gchinellato/Self-Balance-Robot/Arduino/Examples/IMU/Barom/GY80_BMP085.cpp

// Programa : Teste BMP085 - Barometro / temperatura
// Adaptacoes : Arduino e Cia

/*Based largely on code by  Jim Lindblom
 Get pressure, altitude, and temperature from the BMP085.
 Serial.print it out at 9600 baud to serial monitor.
*/

#include <Wire.h>

//Define o endereco I2C do BMP085 - 0x77 ou 119 em decimal
#define BMP085_ADDRESS 0x77  

const unsigned char OSS = 0;  // Oversampling Setting

// Calibration values
int ac1;
int ac2;
int ac3;
unsigned int ac4;
unsigned int ac5;
unsigned int ac6;
int b1;
int b2;
int mb;
int mc;
int md;

// b5 is calculated in bmp085GetTemperature(...), this 
// variable is also used in bmp085GetPressure(...)
// so ...Temperature(...) must be called before ...Pressure(...).
long b5; 

void setup()
{
  Serial.begin(9600);
  Wire.begin();
  // Inicializa o BMP085
  bmp085Calibration();
}

void loop()
{
  // Chama a rotina que calcula a temperatura
  // Esta rotina DEVE ser executada primeiro
  float temperature = bmp085GetTemperature(bmp085ReadUT());
  // Chama a rotina que calcula a pressao
  float pressure = bmp085GetPressure(bmp085ReadUP());
  // Chama a rotina que calcula atmosfera
  float atm = pressure / 101325; 
  // Chama a rotina que calcula a altitude
  float altitude = calcAltitude(pressure); 

  Serial.print("Temperatura: ");
  // Mostra a temperatura com 2 casas decimais
  Serial.print(temperature, 2); 
  Serial.println(" C");

  Serial.print("Pressao: ");
  Serial.print(pressure, 0); 
  Serial.println(" Pa");

  Serial.print("Atmosfera padrao : ");
  // Mostra o valor com 4 casas decimais
  Serial.println(atm, 4); //display 4 decimal places

  Serial.print("Altitude: ");
  // Mostra o valor com 2 casas decimais
  Serial.print(altitude, 2); 
  Serial.println(" M");

  Serial.println();

  //Aguarda 5 segundos e reinicia o processo
  delay(5000);
}

// Armazena todos os valores de calibracao do BMP085 em 
// variaveis globais. Valores de calibracao sao exigidos para
// calcular temperatura e pressao
// Esta funcao deve ser chamada/acionada no inicio do programa
void bmp085Calibration()
{
  ac1 = bmp085ReadInt(0xAA);
  ac2 = bmp085ReadInt(0xAC);
  ac3 = bmp085ReadInt(0xAE);
  ac4 = bmp085ReadInt(0xB0);
  ac5 = bmp085ReadInt(0xB2);
  ac6 = bmp085ReadInt(0xB4);
  b1 = bmp085ReadInt(0xB6);
  b2 = bmp085ReadInt(0xB8);
  mb = bmp085ReadInt(0xBA);
  mc = bmp085ReadInt(0xBC);
  md = bmp085ReadInt(0xBE);
}

// Calcula a temperatura em graus C
float bmp085GetTemperature(unsigned int ut)
{
  long x1, x2;

  x1 = (((long)ut - (long)ac6)*(long)ac5) >> 15;
  x2 = ((long)mc << 11)/(x1 + md);
  b5 = x1 + x2;

  float temp = ((b5 + 8)>>4);
  temp = temp /10;

  return temp;
}

// Calcula a pressao. Os valores de calibracao devem ser conhecidos
// b5 tambem eh exigido, logo a funcao bmp085GetTemperature(...) deve
// ser executada primeiro.
// Funcao retorna pressao em unidades de Pa
long bmp085GetPressure(unsigned long up){
  long x1, x2, x3, b3, b6, p;
  unsigned long b4, b7;

  b6 = b5 - 4000;
  // Calcula B3
  x1 = (b2 * (b6 * b6)>>12)>>11;
  x2 = (ac2 * b6)>>11;
  x3 = x1 + x2;
  b3 = (((((long)ac1)*4 + x3)<<OSS) + 2)>>2;

  // Calcula B4
  x1 = (ac3 * b6)>>13;
  x2 = (b1 * ((b6 * b6)>>12))>>16;
  x3 = ((x1 + x2) + 2)>>2;
  b4 = (ac4 * (unsigned long)(x3 + 32768))>>15;

  b7 = ((unsigned long)(up - b3) * (50000>>OSS));
  if (b7 < 0x80000000)
    p = (b7<<1)/b4;
  else
    p = (b7/b4)<<1;

  x1 = (p>>8) * (p>>8);
  x1 = (x1 * 3038)>>16;
  x2 = (-7357 * p)>>16;
  p += (x1 + x2 + 3791)>>4;

  long temp = p;
  return temp;
}

// Read 1 byte from the BMP085 at 'address'
char bmp085Read(unsigned char address)
{
  unsigned char data;

  Wire.beginTransmission(BMP085_ADDRESS);
  Wire.write(address);
  Wire.endTransmission();

  Wire.requestFrom(BMP085_ADDRESS, 1);
  while(!Wire.available())
    ;

  return Wire.read();
}

// Read 2 bytes from the BMP085
// First byte will be from 'address'
// Second byte will be from 'address'+1
int bmp085ReadInt(unsigned char address)
{
  unsigned char msb, lsb;

  Wire.beginTransmission(BMP085_ADDRESS);
  Wire.write(address);
  Wire.endTransmission();

  Wire.requestFrom(BMP085_ADDRESS, 2);
  while(Wire.available()<2)
    ;
  msb = Wire.read();
  lsb = Wire.read();

  return (int) msb<<8 | lsb;
}

// Read the uncompensated temperature value
unsigned int bmp085ReadUT(){
  unsigned int ut;

  // Write 0x2E into Register 0xF4
  // This requests a temperature reading
  Wire.beginTransmission(BMP085_ADDRESS);
  Wire.write(0xF4);
  Wire.write(0x2E);
  Wire.endTransmission();

  // Wait at least 4.5ms
  delay(5);

  // Read two bytes from registers 0xF6 and 0xF7
  ut = bmp085ReadInt(0xF6);
  return ut;
}

// Read the uncompensated pressure value
unsigned long bmp085ReadUP(){

  unsigned char msb, lsb, xlsb;
  unsigned long up = 0;

  // Write 0x34+(OSS<<6) into register 0xF4
  // Request a pressure reading w/ oversampling setting
  Wire.beginTransmission(BMP085_ADDRESS);
  Wire.write(0xF4);
  Wire.write(0x34 + (OSS<<6));
  Wire.endTransmission();

  // Wait for conversion, delay time dependent on OSS
  delay(2 + (3<<OSS));

  // Read register 0xF6 (MSB), 0xF7 (LSB), and 0xF8 (XLSB)
  msb = bmp085Read(0xF6);
  lsb = bmp085Read(0xF7);
  xlsb = bmp085Read(0xF8);

  up = (((unsigned long) msb << 16) | ((unsigned long) lsb << 8) | (unsigned long) xlsb) >> (8-OSS);

  return up;
}

void writeRegister(int deviceAddress, byte address, byte val) {
  Wire.beginTransmission(deviceAddress); // start transmission to device 
  Wire.write(address);       // send register address
  Wire.write(val);         // send value to write
  Wire.endTransmission();     // end transmission
}

int readRegister(int deviceAddress, byte address){

  int v;
  Wire.beginTransmission(deviceAddress);
  Wire.write(address); // register to read
  Wire.endTransmission();

  Wire.requestFrom(deviceAddress, 1); // read a byte

  while(!Wire.available()) {
    // waiting
  }

  v = Wire.read();
  return v;
}

float calcAltitude(float pressure)
{
  float A = pressure/101325;
  float B = 1/5.25588;
  float C = pow(A,B);
  C = 1 - C;
  C = C /0.0000225577;

  return C;
}
