gchinellato/Self-Balance-Robot/nfs-server/modules/ComputerVison/Test/stream.py

#!/usr/bin/python

import cv2
import urllib
import numpy as np
 
stream=urllib.urlopen('http://192.168.1.49:8080/?action=stream')
bytes=''
while True:
    bytes+=stream.read(1024)
    a = bytes.find('\xff\xd8')
    b = bytes.find('\xff\xd9')
    if a!=-1 and b!=-1:
        jpg = bytes[a:b+2]
        bytes= bytes[b+2:]
        i = cv2.imdecode(np.fromstring(jpg, dtype=np.uint8),cv2.CV_LOAD_IMAGE_COLOR)
        cv2.imshow('i',i)
        if cv2.waitKey(1) == 27:
            exit(0)
