gchinellato/Self-Balance-Robot/examples/raspi/i2c-sensors/bitify/python/web/server.py

#!/usr/bin/env python

import web  # web.py
import smbus

import bitify.python.sensors.imu as imu
from bitify.python.utils.i2cutils import i2c_raspberry_pi_bus_number

urls = (
    '/', 'index'
)

bus = smbus.SMBus(i2c_raspberry_pi_bus_number())
imu_controller = imu.IMU(bus, 0x69, 0x53, 0x1e, "IMU")

imu_controller.set_compass_offsets(9, -10, -140)

app = web.application(urls, globals())

class index:
    def GET(self):
        (pitch, roll, yaw) = imu_controller.read_pitch_roll_yaw()
        result = "%.2f %.2f %.2f" % (pitch, roll, yaw)
        return result

if __name__ == "__main__":
    app.run()
