gchinellato/Self-Balance-Robot/nfs-server/modules/PanTilt/Test/wiringPi-test.py

#!/usr/bin/python

import wiringpi
import time

#GPIO_WIRING_PIN = 1 # gpio pin 12 = wiringpi no. 1 (BCM 18)
GPIO_BCM = 18

#Initialize HW PWM
#wiringpi.wiringPiSetup()
#wiringpi.pinMode(GPIO_BCM, 2)     # PWM mode
#wiringpi.pwmWrite(GPIO_BCM, 0)    # OFF

#Initialize SW PWM
wiringpi.wiringPiSetupGpio()
wiringpi.pinMode(GPIO_BCM, 2)     # PWM mode
wiringpi.softPwmCreate(GPIO_BCM,0,200) # Setup PWM using Pin, Initial Value and Range parameters

# Set PWM
def pwm(value):
    #HW PWM
    #wiringpi.pwmWrite(GPIO_BCM, value)
    #SW PWM
    wiringpi.softPwmWrite(GPIO_BCM, value)

print "PWM 0"
for i in range(5,18):
    pwm(i)
    print i
    time.sleep(1)
pwm(0)
