gchinellato/Self-Balance-Robot/nfs-server/modules/ComputerVison/Test/test-cv.py

#!/usr/bin/python

import numpy as np
from matplotlib import pyplot as plt
from picamera.array import PiRGBArray
from picamera import PiCamera
import time
import cv2

'''# Load an color image in grayscale or color
img = cv2.imread('bravus.jpg', 0)
plt.imshow(img, cmap = 'gray', interpolation = 'bicubic')
plt.xticks([]), plt.yticks([])  # to hide tick values on X and Y axis
plt.show()

cv2.namedWindow('image', cv2.WINDOW_NORMAL)
cv2.imshow('image', img)
cv2.waitKey(0)
cv2.destroyAllWindows()'''
 
# initialize the camera and grab a reference to the raw camera capture
camera = PiCamera()
camera.resolution = (640, 480)
camera.framerate = 32
rawCapture = PiRGBArray(camera, size=(640, 480))
 
# allow the camera to warmup
time.sleep(0.1)
 
# capture frames from the camera
for frame in camera.capture_continuous(rawCapture, format="bgr", use_video_port=True):

	# grab the raw NumPy array representing the image, then initialize the timestamp
	# and occupied/unoccupied text
    image = frame.array
    print image
 
	# show the frame
    cv2.imshow("Frame", image)
    key = cv2.waitKey(10) & 0xFF
 
	# clear the stream in preparation for the next frame
    rawCapture.truncate(0)
 
	# if the `q` key was pressed, break from the loop
    if key == ord("q"):
    	break
